zakqwy/cyborg_ring/img/cyborg_ring_pcb_top.jpg

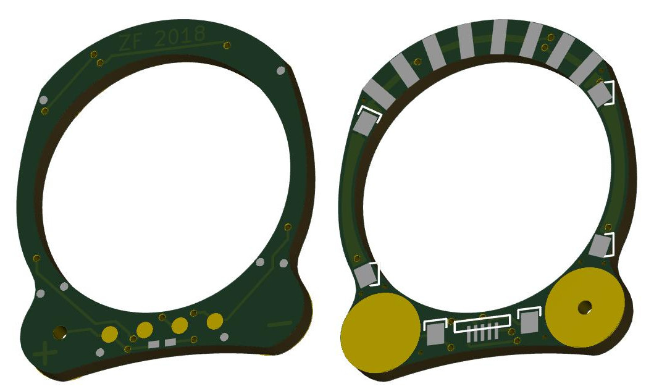
img/cyborg_ring_pcb_top.jpg
